soligen2010/CurveTracerControl/QuickStats.h

/* QuickStats.h - Library for quick descriptive statistics of an array samples[] of size m,
* assuming a normal distribution.
* Created by David Dubins, January 10th, 2016.
* Released into the public domain.
*/
 
#ifndef QuickStats_h
#define QuickStats_h
 
#include <Arduino.h>
 
class QuickStats {
public:
QuickStats();
~QuickStats();
float average(float samples[],int m);
float fabs(float sample);
float g_average(float samples[],int m);
float minimum(float samples[],int m);
float maximum(float samples[],int m);
float stdev(float samples[],int m);
float stderror(float samples[],int m);
float CV(float samples[],int m);
void bubbleSort(float A[],int len);
float median(float samples[],int m);
float mode(float samples[],int m,float epsilon);
float slope(float x[],float samples[],int m);
float intercept(float x[],float samples[],int m);
void filternan(float samples[],int &m);
void f_round(float samples[], int, int);
};
 
#endif
//END OF FILE
